RafaelRiber/R2Quadcopter-Hardware/Images/IMG_5318.JPG

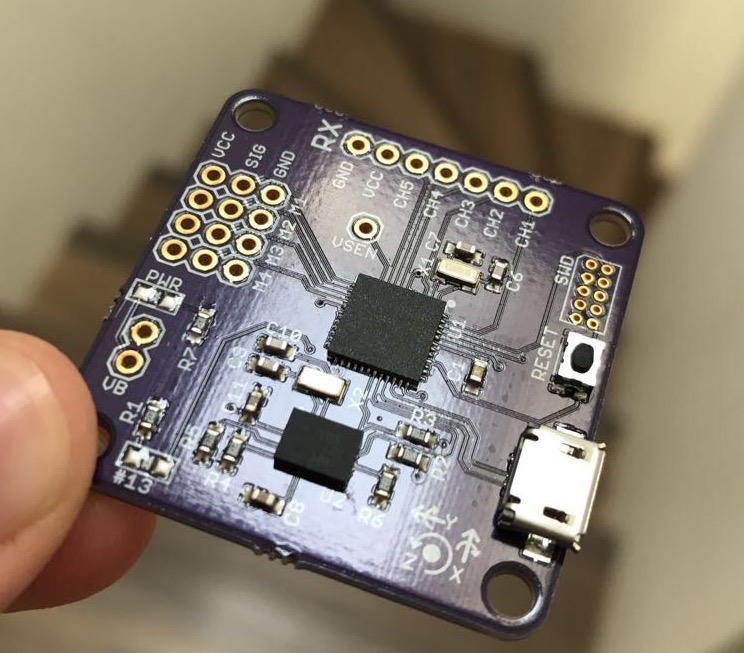
Images/IMG_5318.JPG
